LucasGarcia0924/Echo-Wave/Evidencias/ESP32 quemada.jpg

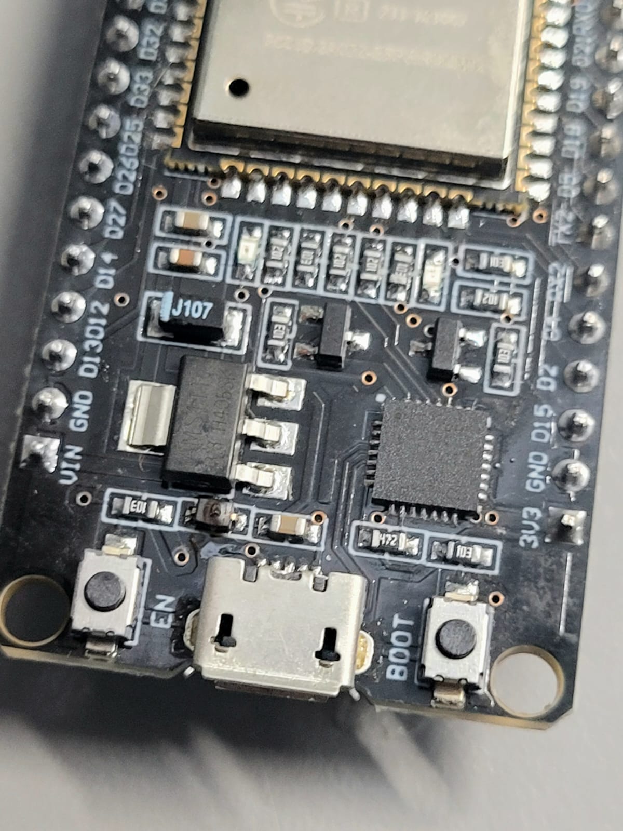
Evidencias/ESP32 quemada.jpg
