LucasGarcia0924/Echo-Wave/Evidencias/Piezas corte laser.jpg

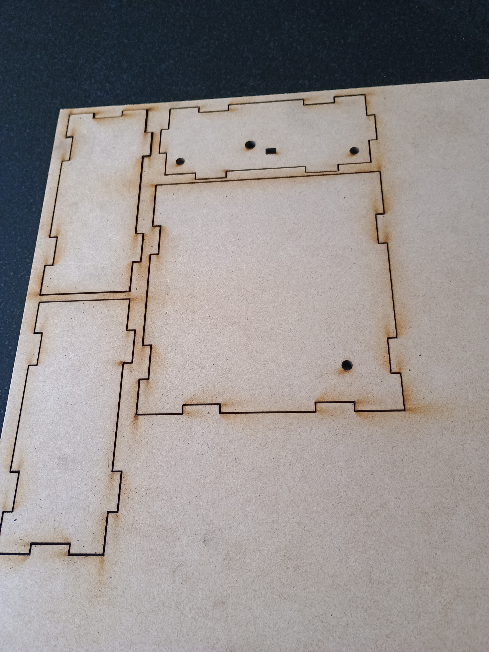
Evidencias/Piezas corte laser.jpg
