LucasGarcia0924/Echo-Wave/Evidencias/Programacion2.jpg

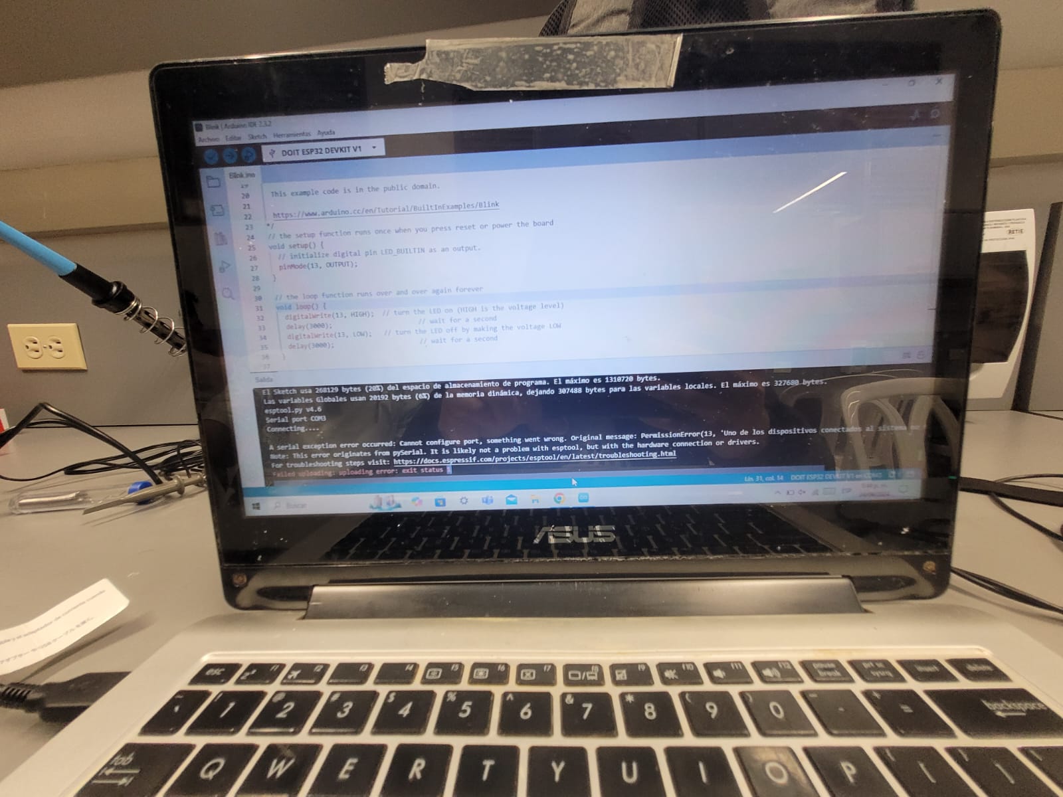
Evidencias/Programacion2.jpg
