LucasGarcia0924/Echo-Wave/Evidencias/Programación.jpg

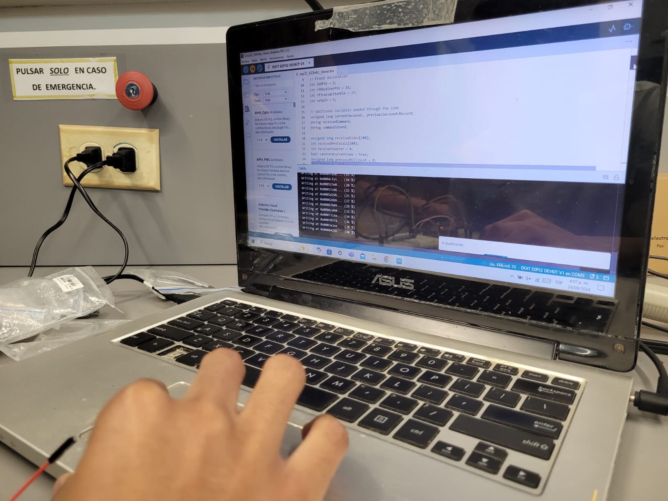
Evidencias/Programación.jpg
