LucasGarcia0924/Echo-Wave/Evidencias/Soldadura.jpg

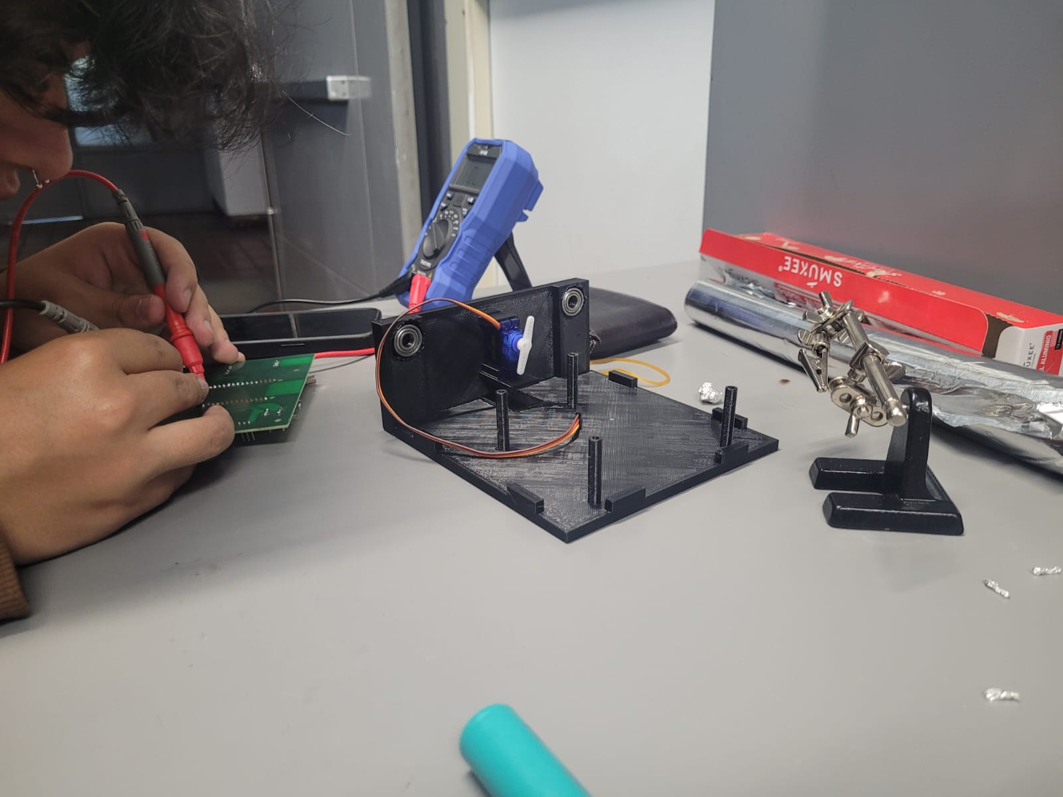
Evidencias/Soldadura.jpg
