LucasGarcia0924/Echo-Wave/Imagenes/blackbox.jpg

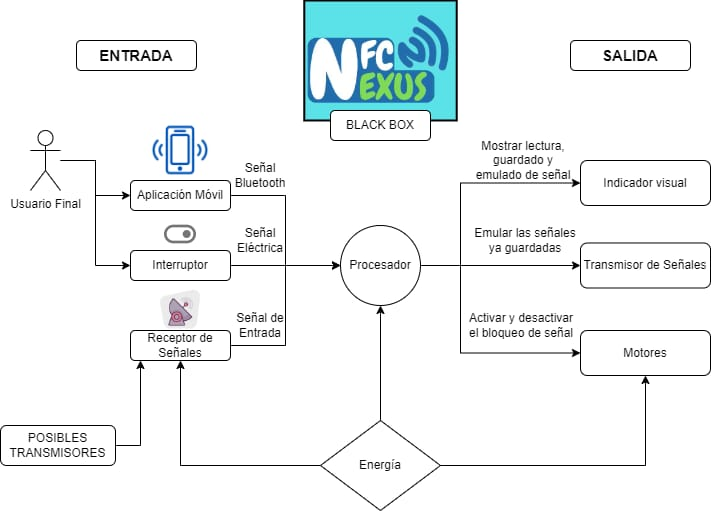
Imagenes/blackbox.jpg
