LucasGarcia0924/Echo-Wave/Imagenes/Completo.png

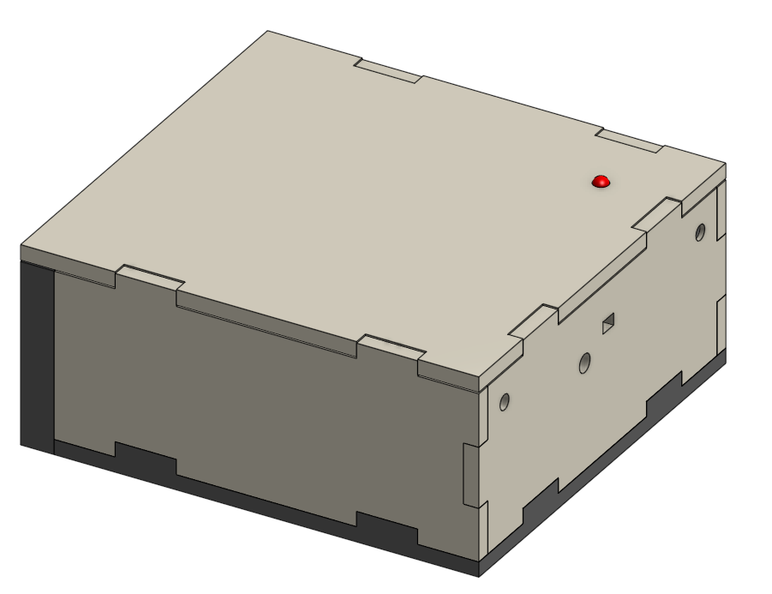
Imagenes/Completo.png
