LucasGarcia0924/Echo-Wave/Imagenes/Diagrama Tecnologico.png

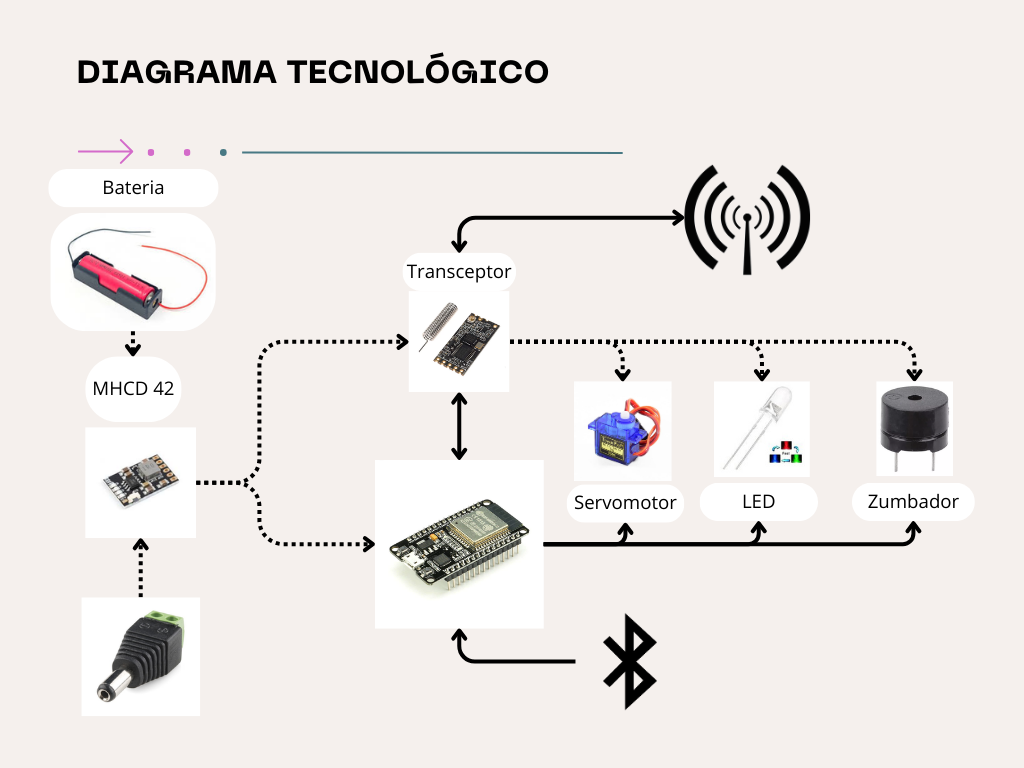
Imagenes/Diagrama Tecnologico.png
