LucasGarcia0924/Echo-Wave/Imagenes/Echowave por dentro.png

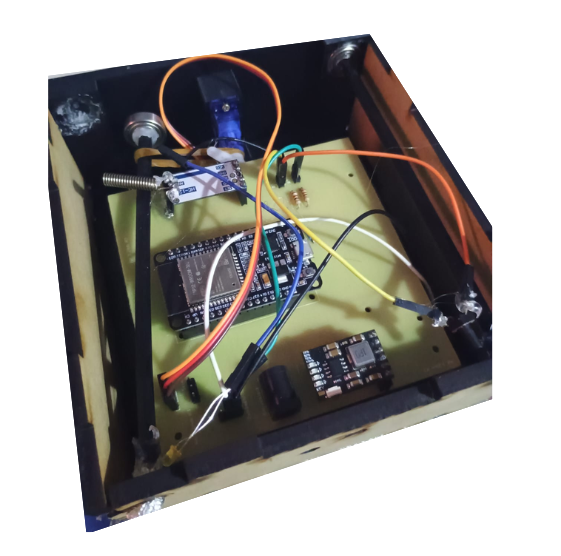
Imagenes/Echowave por dentro.png
