LucasGarcia0924/Echo-Wave/Imagenes/EchoWave.png

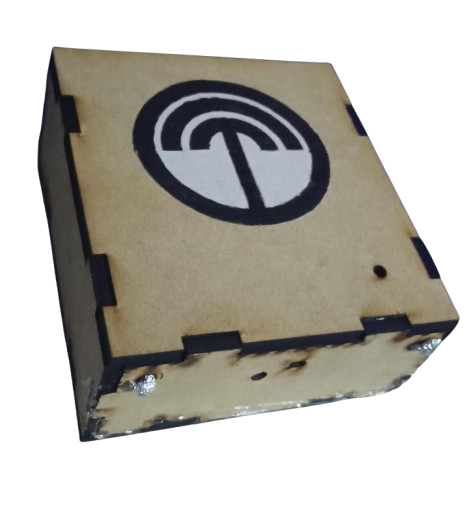
Imagenes/EchoWave.png
