LucasGarcia0924/Echo-Wave/Imagenes/Estable.png

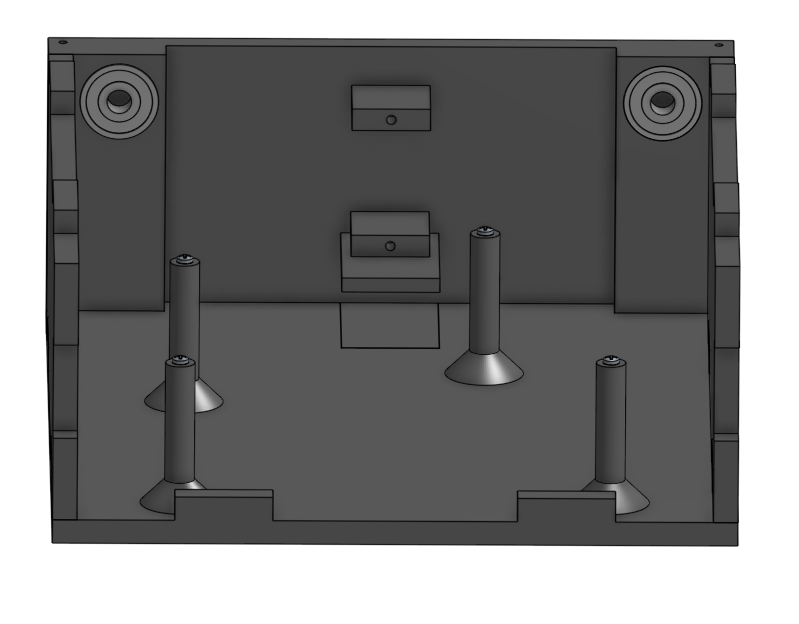
Imagenes/Estable.png
