LucasGarcia0924/Echo-Wave/Imagenes/Grafica Diagrama de Flujo Corporativo Juvenil Azul.png

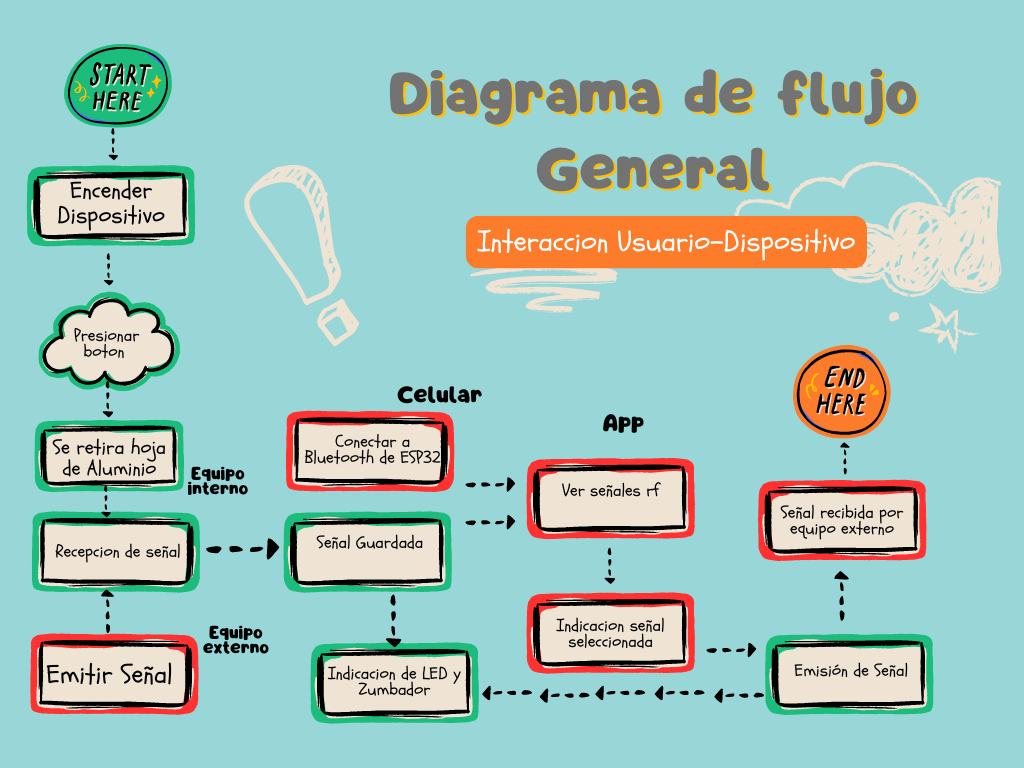
Imagenes/Grafica Diagrama de Flujo Corporativo Juvenil Azul.png
