LucasGarcia0924/Echo-Wave/Imagenes/graybox.jpg

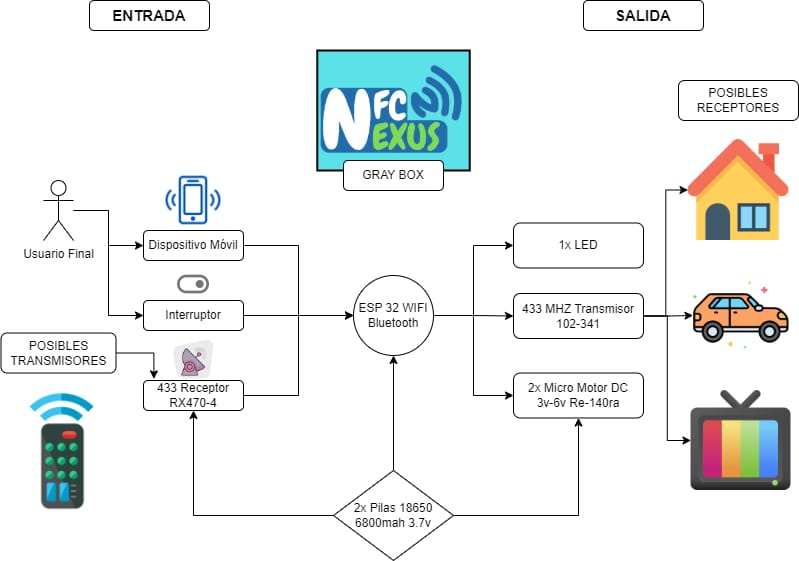
Imagenes/graybox.jpg
