LucasGarcia0924/Echo-Wave/Imagenes/MDF.png

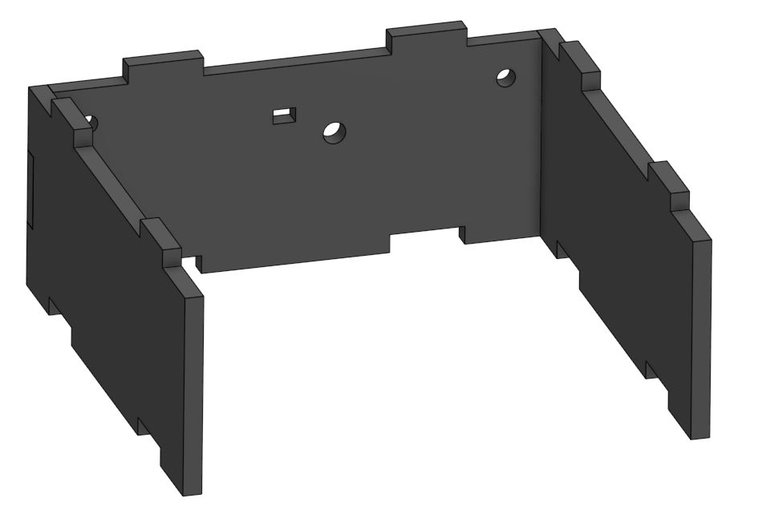
Imagenes/MDF.png
