LucasGarcia0924/Echo-Wave/Imagenes/PCB diseño virtual 1.png

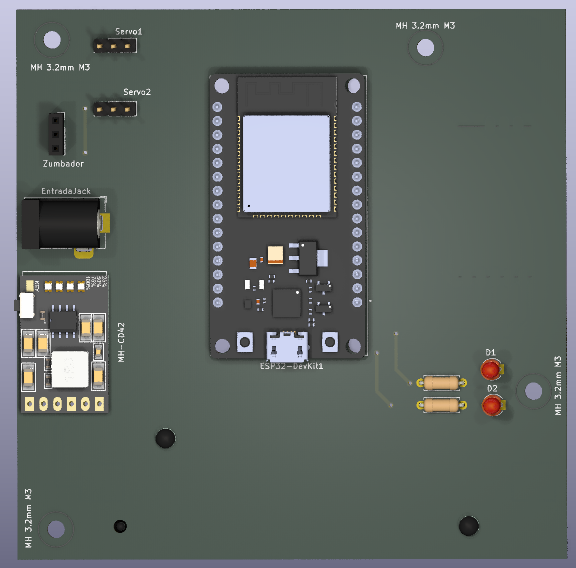
Imagenes/PCB diseño virtual 1.png
