LucasGarcia0924/Echo-Wave/Imagenes/PCB Layout.png

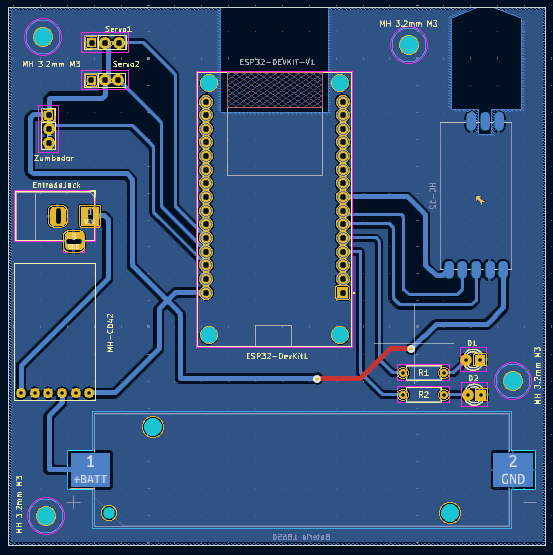
Imagenes/PCB Layout.png
