LucasGarcia0924/Echo-Wave/Imagenes/PCB-conectada alante.jpg

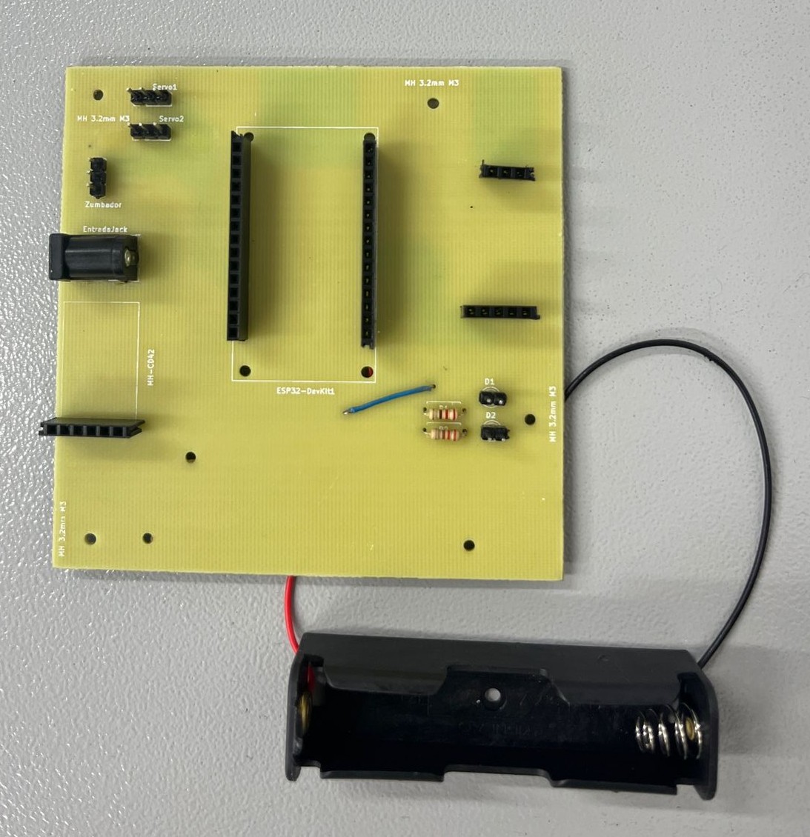
Imagenes/PCB-conectada alante.jpg
