LucasGarcia0924/Echo-Wave/Imagenes/PCB-conectada atras.jpg

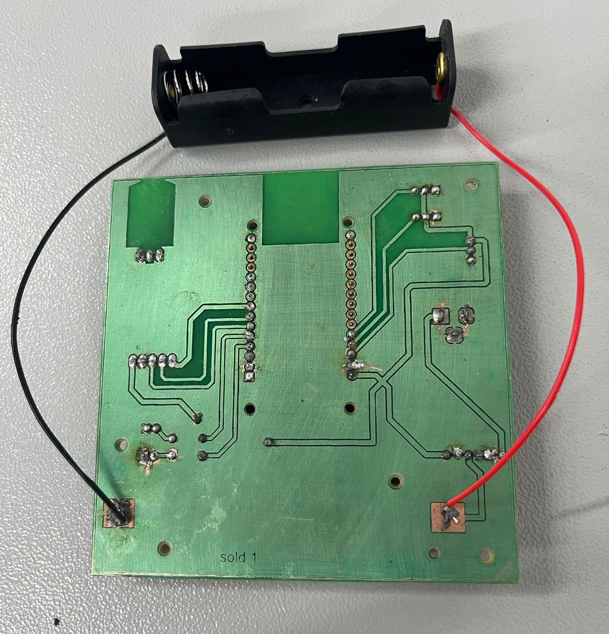
Imagenes/PCB-conectada atras.jpg
