LucasGarcia0924/Echo-Wave/Imagenes/PCB-pordetras.jpg

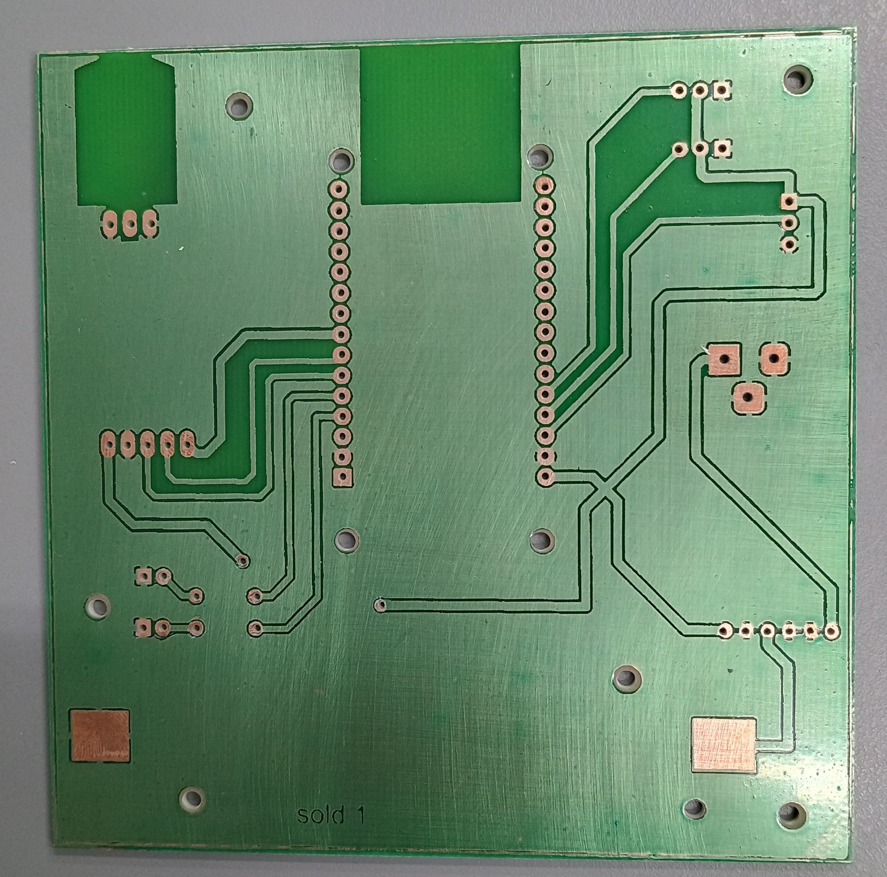
Imagenes/PCB-pordetras.jpg
