LucasGarcia0924/Echo-Wave/Imagenes/PCBporAlante.jpg

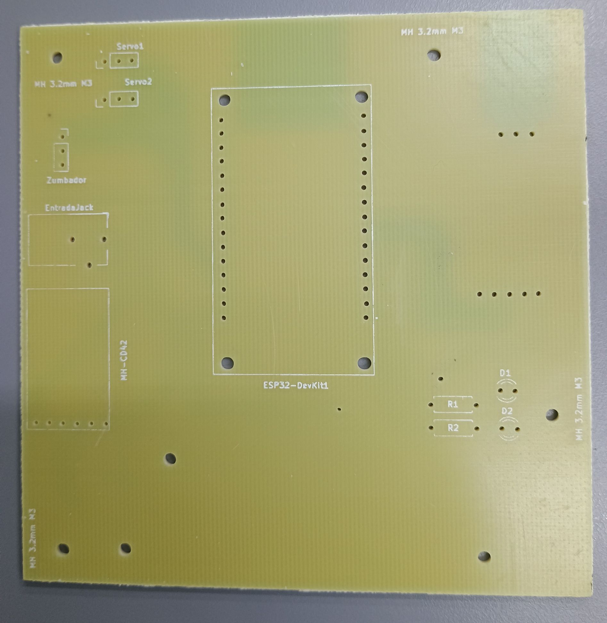
Imagenes/PCBporAlante.jpg
