LucasGarcia0924/Echo-Wave/Imagenes/Screenshot 2024-09-25 095106.png

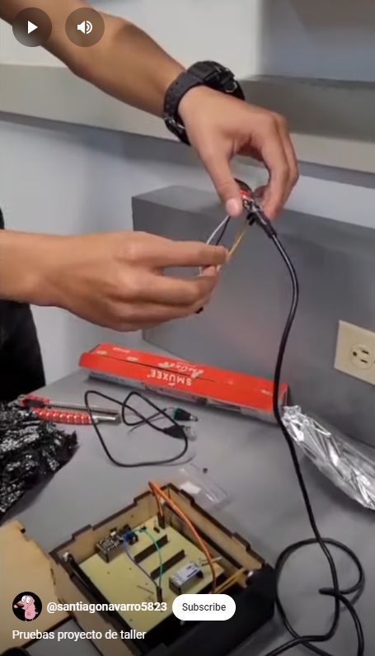
Imagenes/Screenshot 2024-09-25 095106.png
