LucasGarcia0924/Echo-Wave/Imagenes/TLB.png

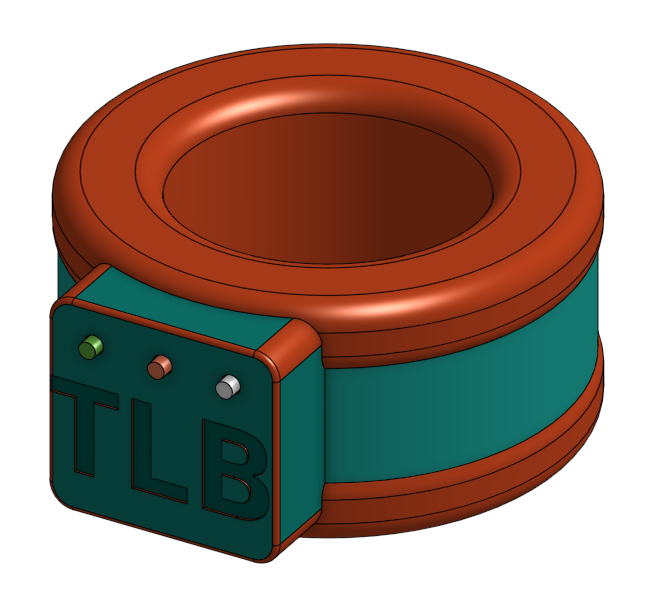
Imagenes/TLB.png
