LucasGarcia0924/Echo-Wave/NFC NEXUS.png

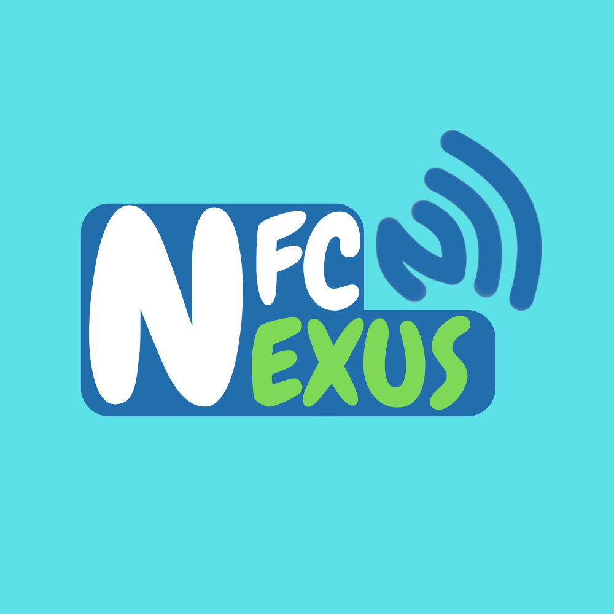
NFC NEXUS.png
