LucasGarcia0924/Echo-Wave/Imagenes/PCB-componentes-02.jpg

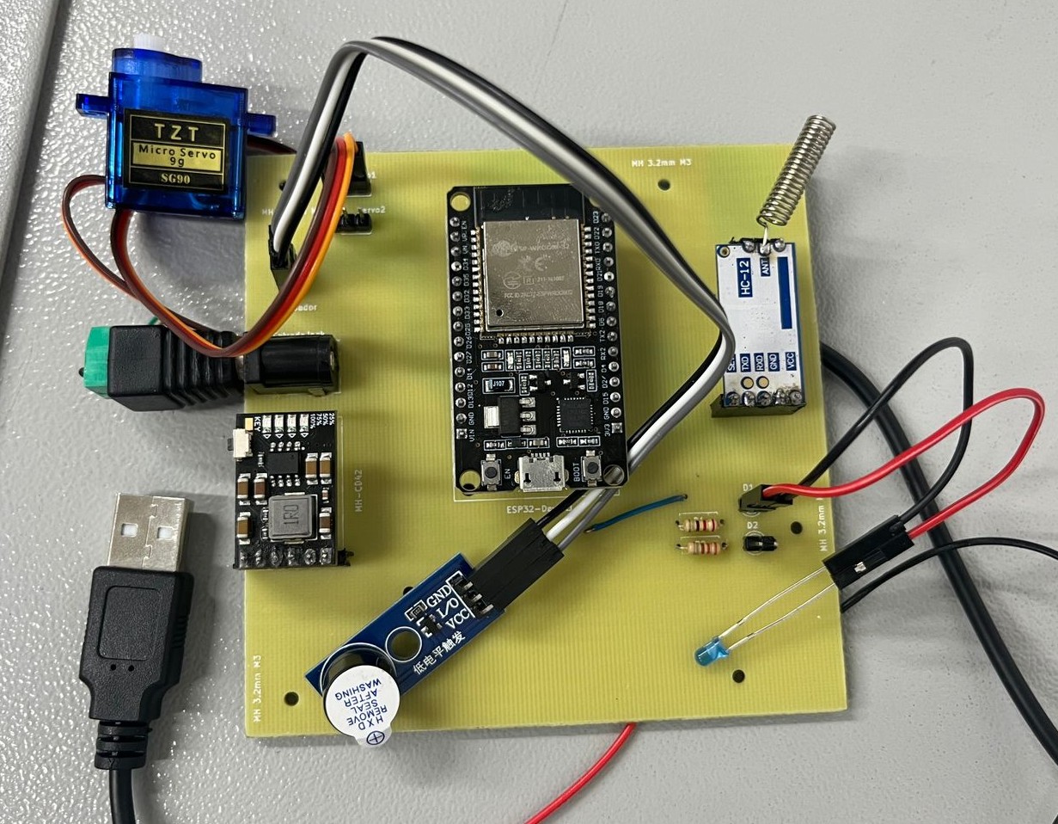
Imagenes/PCB-componentes-02.jpg
