LucasGarcia0924/Echo-Wave/Imagenes/PCB-componentes-04.jpg

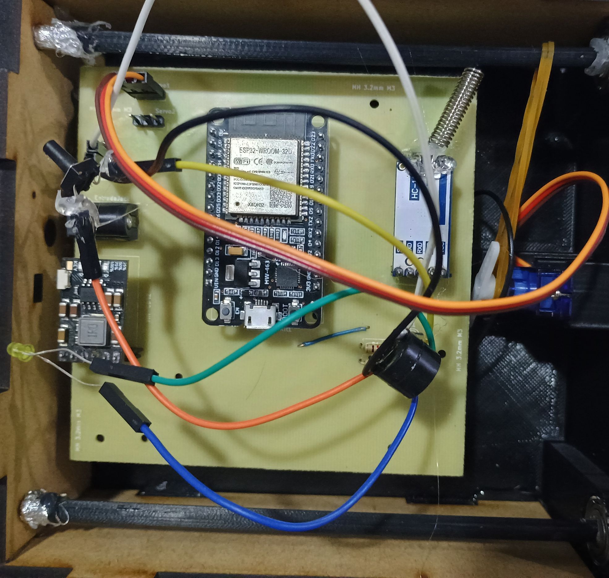
Imagenes/PCB-componentes-04.jpg
