LucasGarcia0924/Echo-Wave/Evidencias/Case ensamblado.jpg

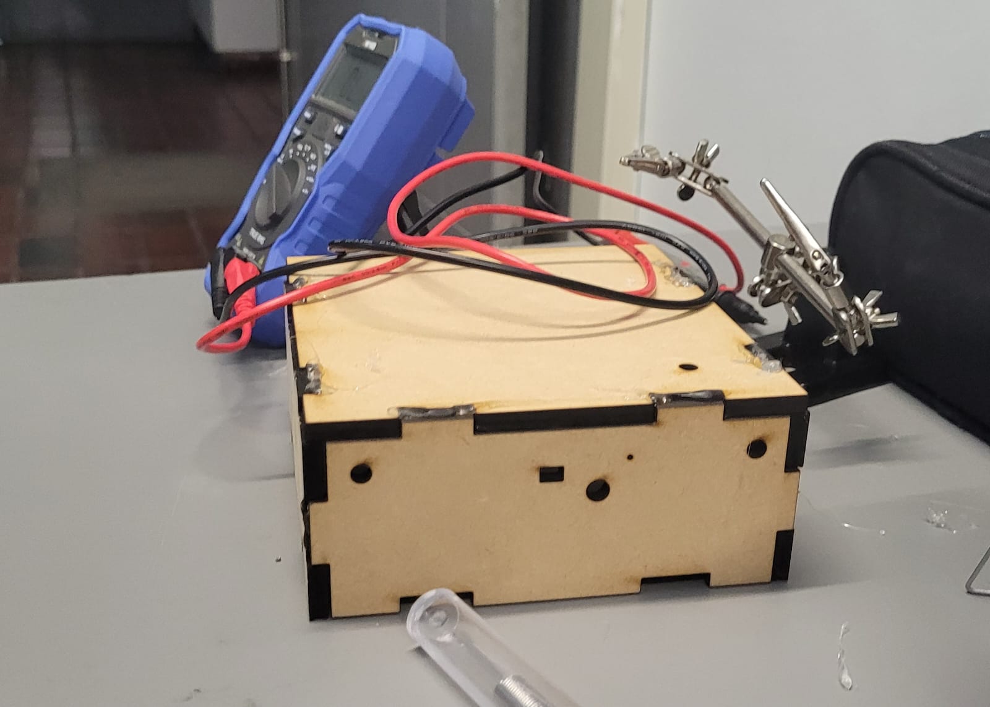
Evidencias/Case ensamblado.jpg
