LucasGarcia0924/Echo-Wave/Evidencias/Montaje1.jpg

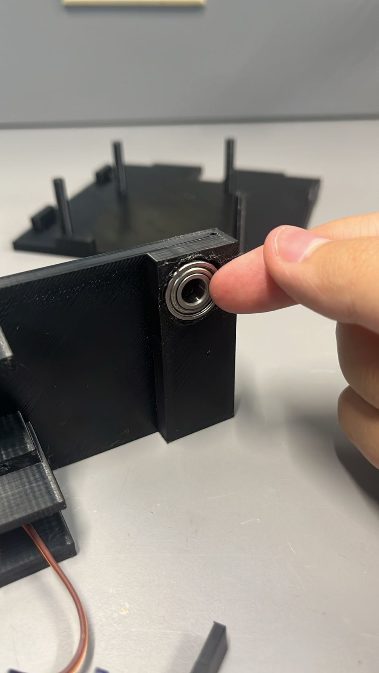
Evidencias/Montaje1.jpg
