LucasGarcia0924/Echo-Wave/Evidencias/Montaje2.jpg

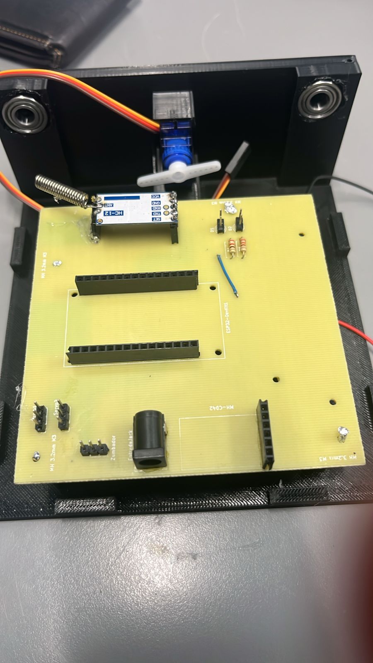
Evidencias/Montaje2.jpg
