LucasGarcia0924/Echo-Wave/Evidencias/Montaje3.jpg

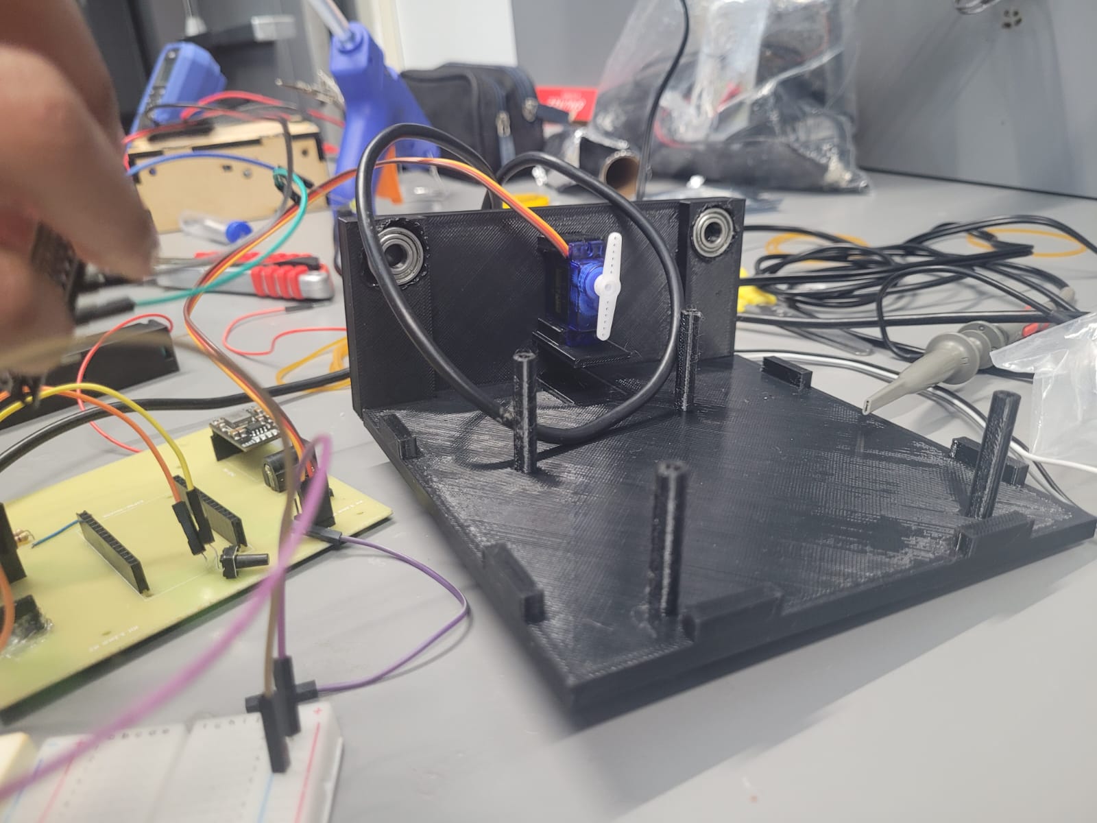
Evidencias/Montaje3.jpg
