LucasGarcia0924/Echo-Wave/Evidencias/Montaje4.jpg

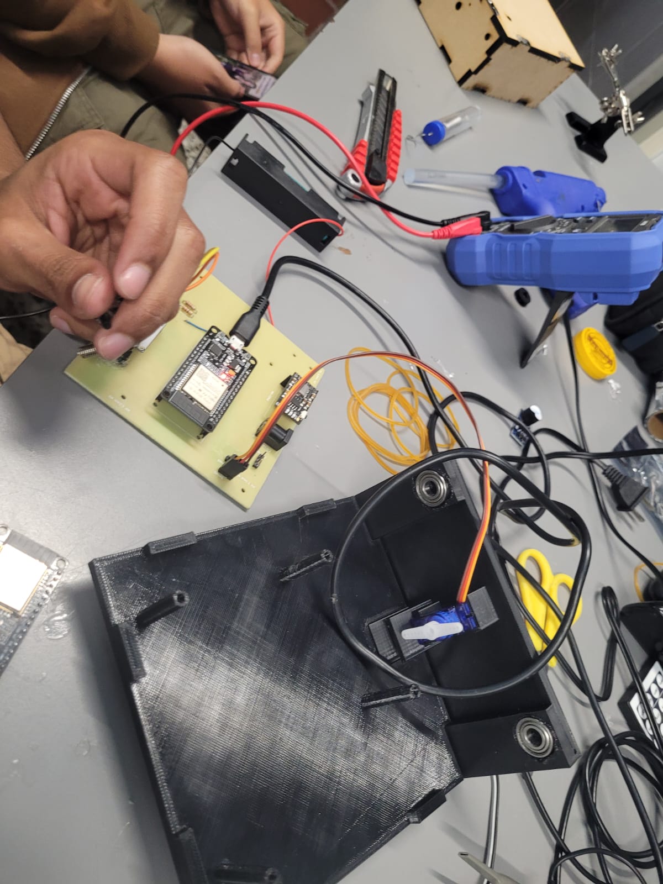
Evidencias/Montaje4.jpg
