LucasGarcia0924/Echo-Wave/Evidencias/Montaje Final por fuera.jpeg

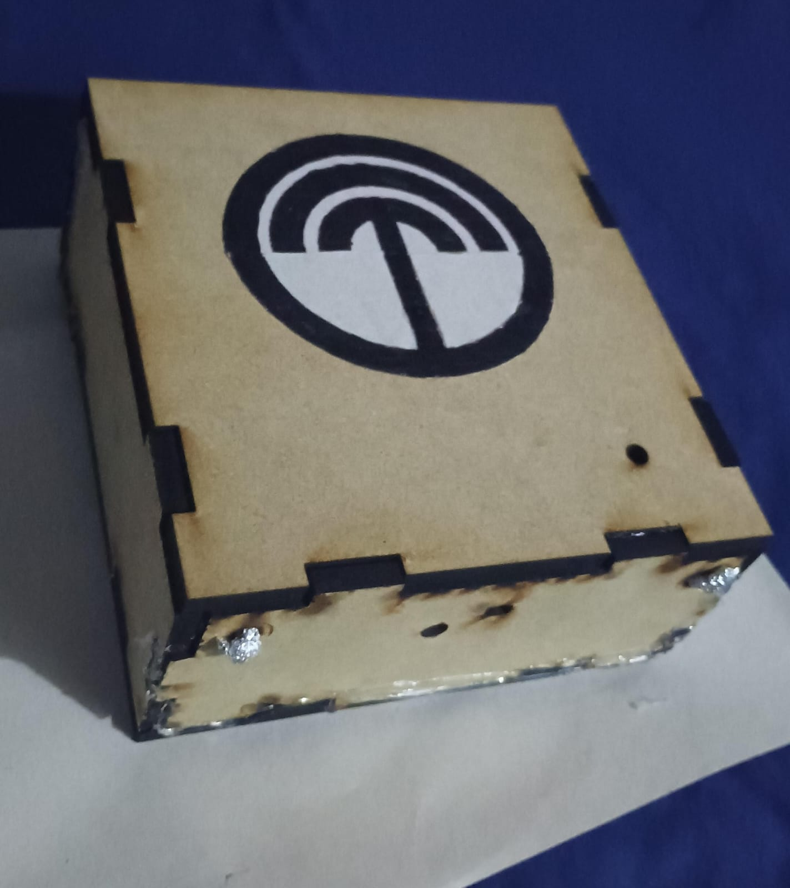
Evidencias/Montaje Final por fuera.jpeg
