LucasGarcia0924/Echo-Wave/Evidencias/Prueba de funcionamiento.jpg

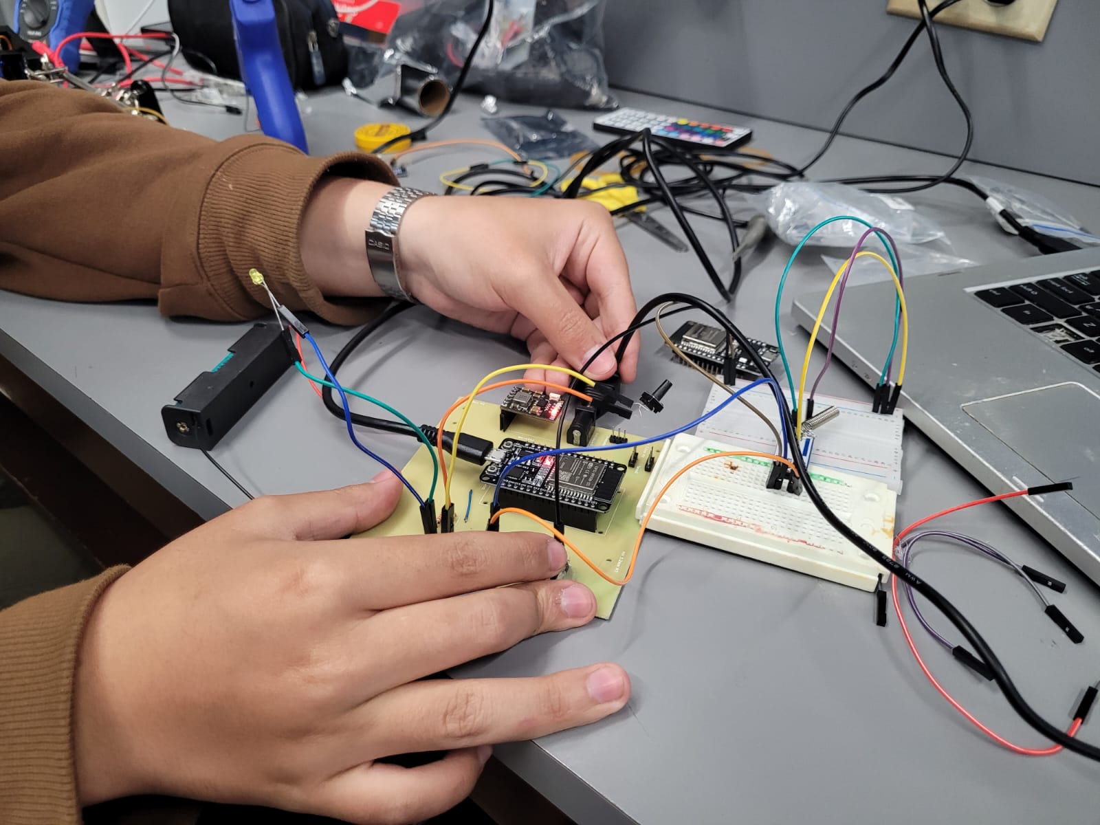
Evidencias/Prueba de funcionamiento.jpg
