LucasGarcia0924/Echo-Wave/Imagenes/QR-Pruebas-EW.png

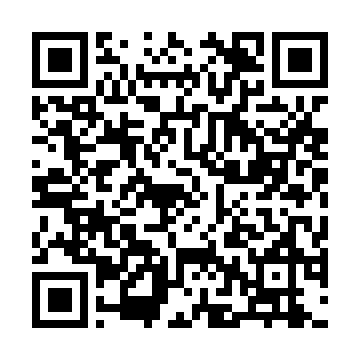
Imagenes/QR-Pruebas-EW.png
